fm4dd/pi-weather/documentation/weather-display-v1.0/images/weather-display-v10-09.jpg

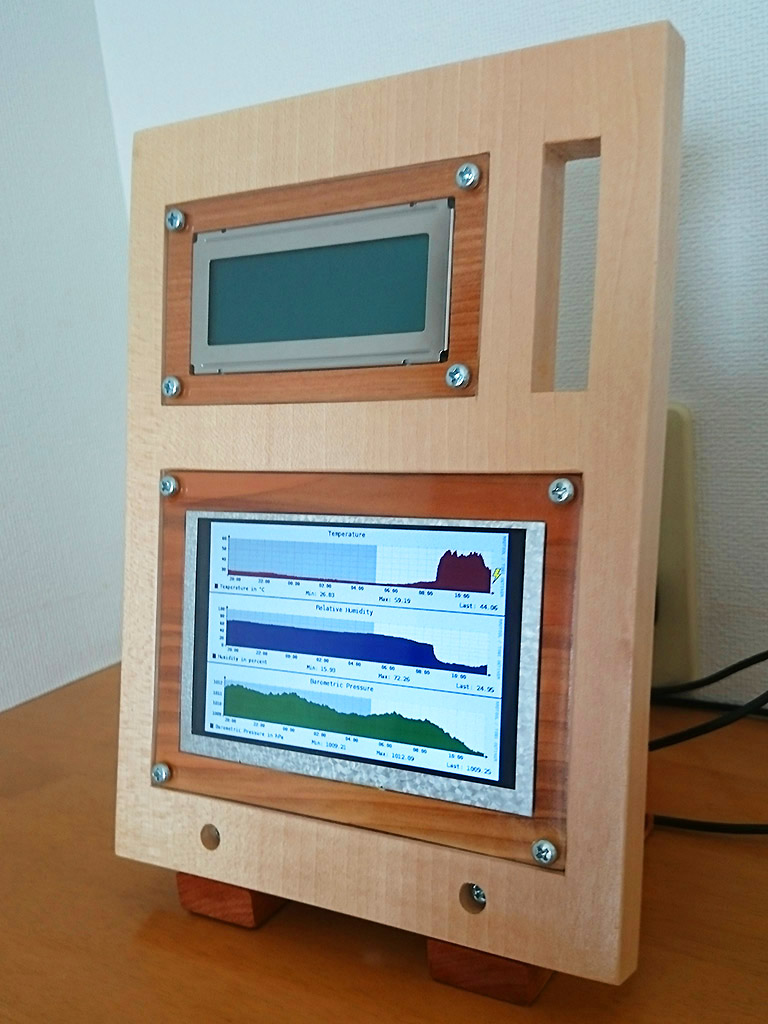
documentation/weather-display-v1.0/images/weather-display-v10-09.jpg
