fm4dd/pi-weather/documentation/weather-station-v1.1/images/weather-station-v11-05.jpg

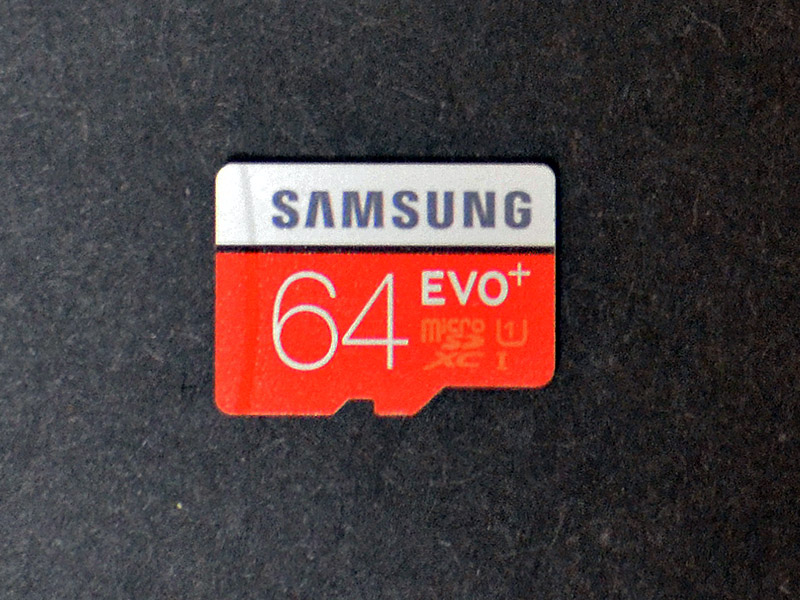
documentation/weather-station-v1.1/images/weather-station-v11-05.jpg
