fm4dd/pi-weather/documentation/weather-web-v1.0/images/weather-web-v10-01.png

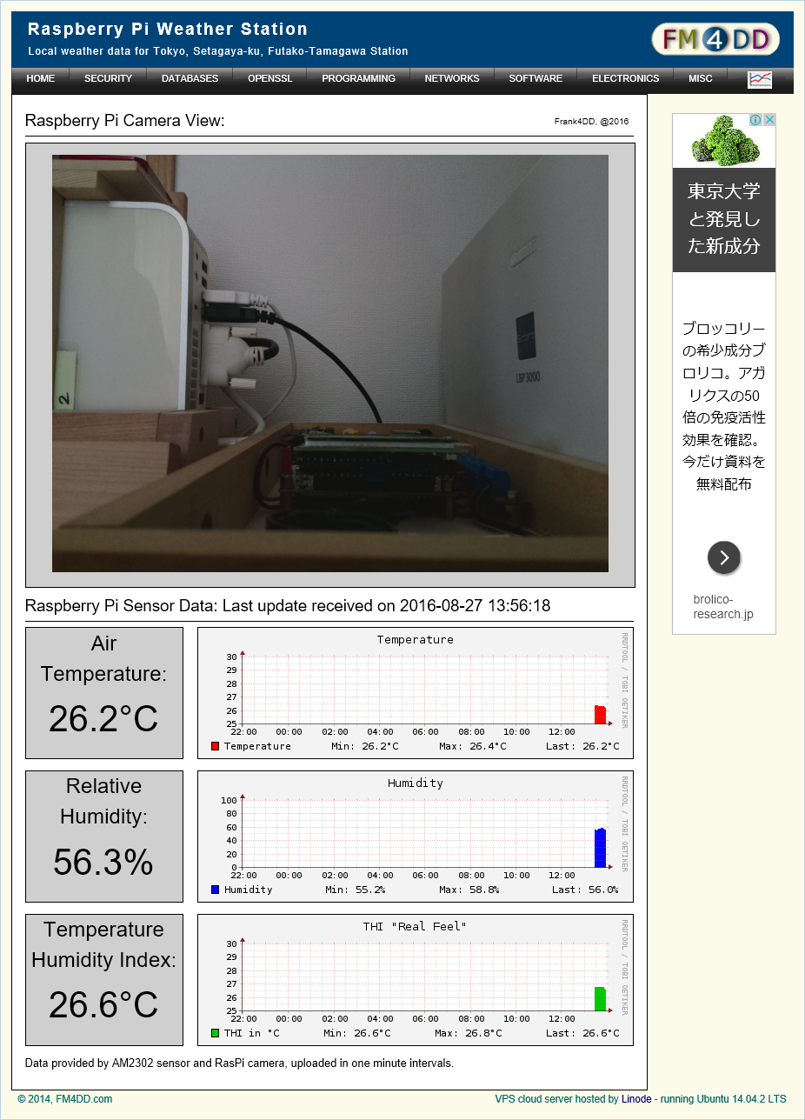
documentation/weather-web-v1.0/images/weather-web-v10-01.png
