fm4dd/pi-weather/weather-display/var/out.png

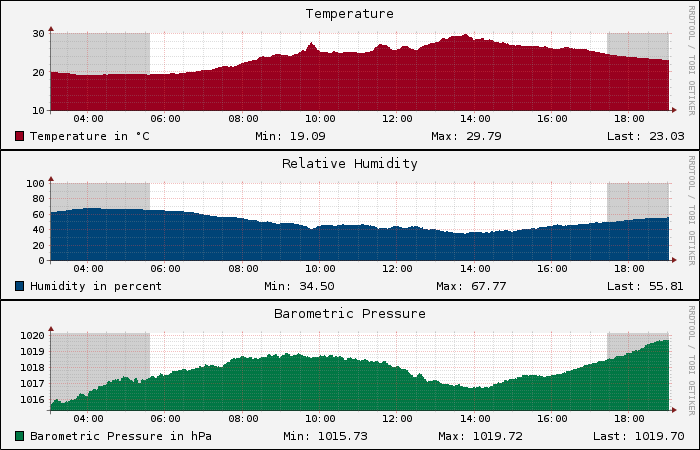
weather-display/var/out.png
