fm4dd/pi-weather/documentation/weather-display-v1.0/cad/05 LCD Frame F and TFT back G v10.dxf

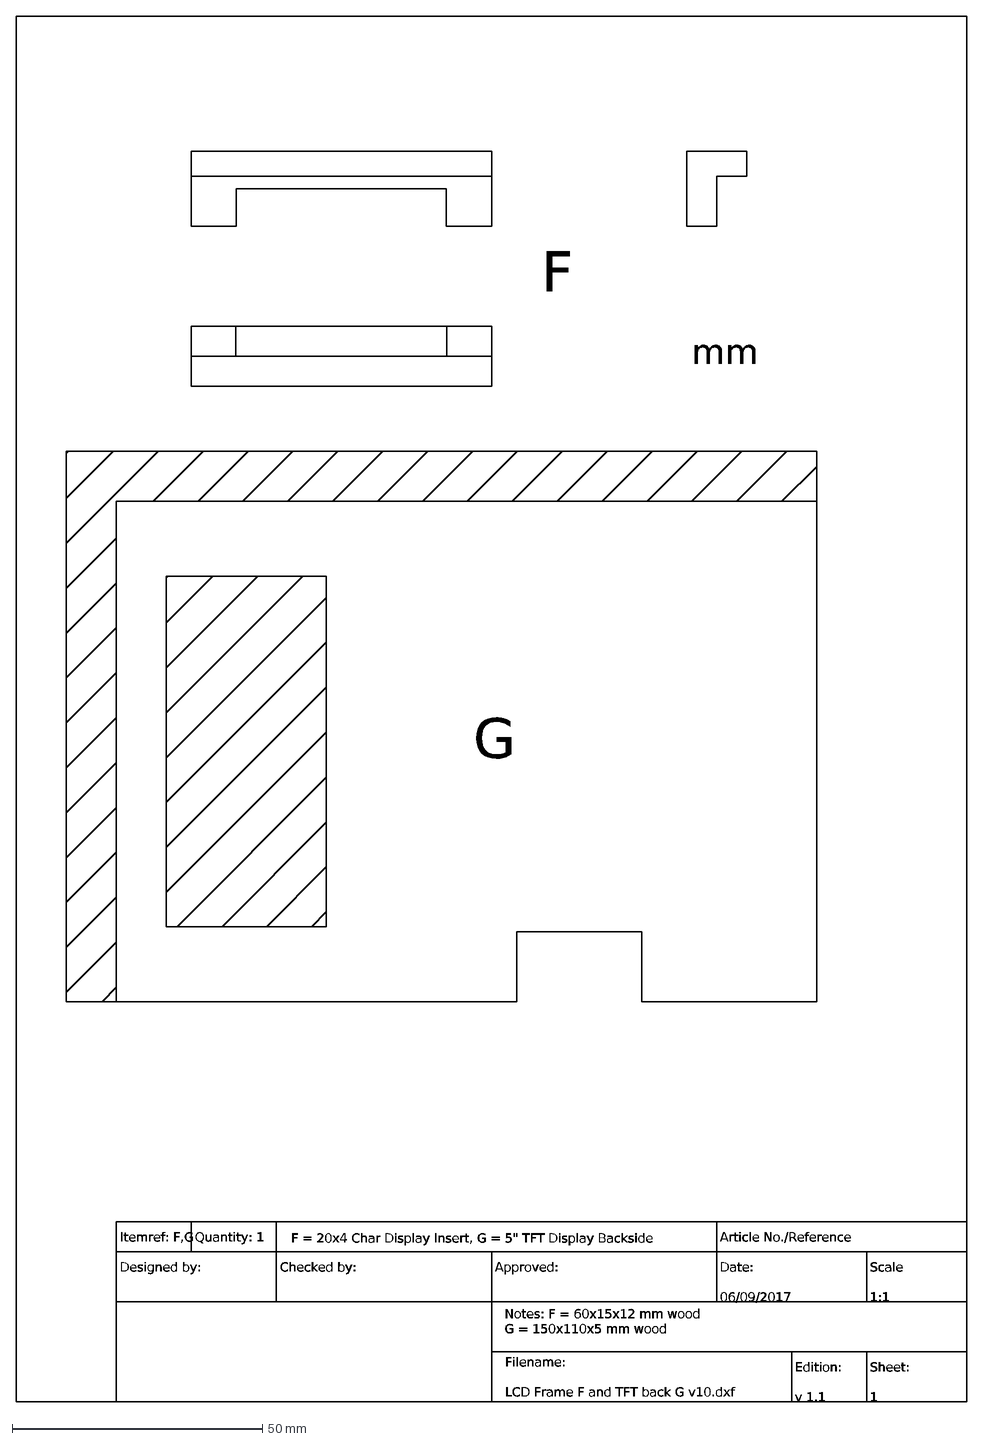
[picture p50: CAD file, 2017-10-29]
documentation/weather-display-v1.0/cad/05 LCD Frame F and TFT back G v10.dxf
Itemref: F,G
Quantity: 1
F = 20x4 Char Display Insert, G = 5" TFT Display Backside
Article No./Reference
Designed by:
Checked by:
Approved:
Filename: LCD Frame F and TFT back G v10.dxf
Date: 06/09/2017
Scale 1:1
Edition: v 1.1
Sheet: 1
Notes: F = 60x15x12 mm wood G = 150x110x5 mm wood
mm
F
G
