fm4dd/pi-weather/documentation/weather-station-v1.1/cad/sensor-frame side detail v11.dxf

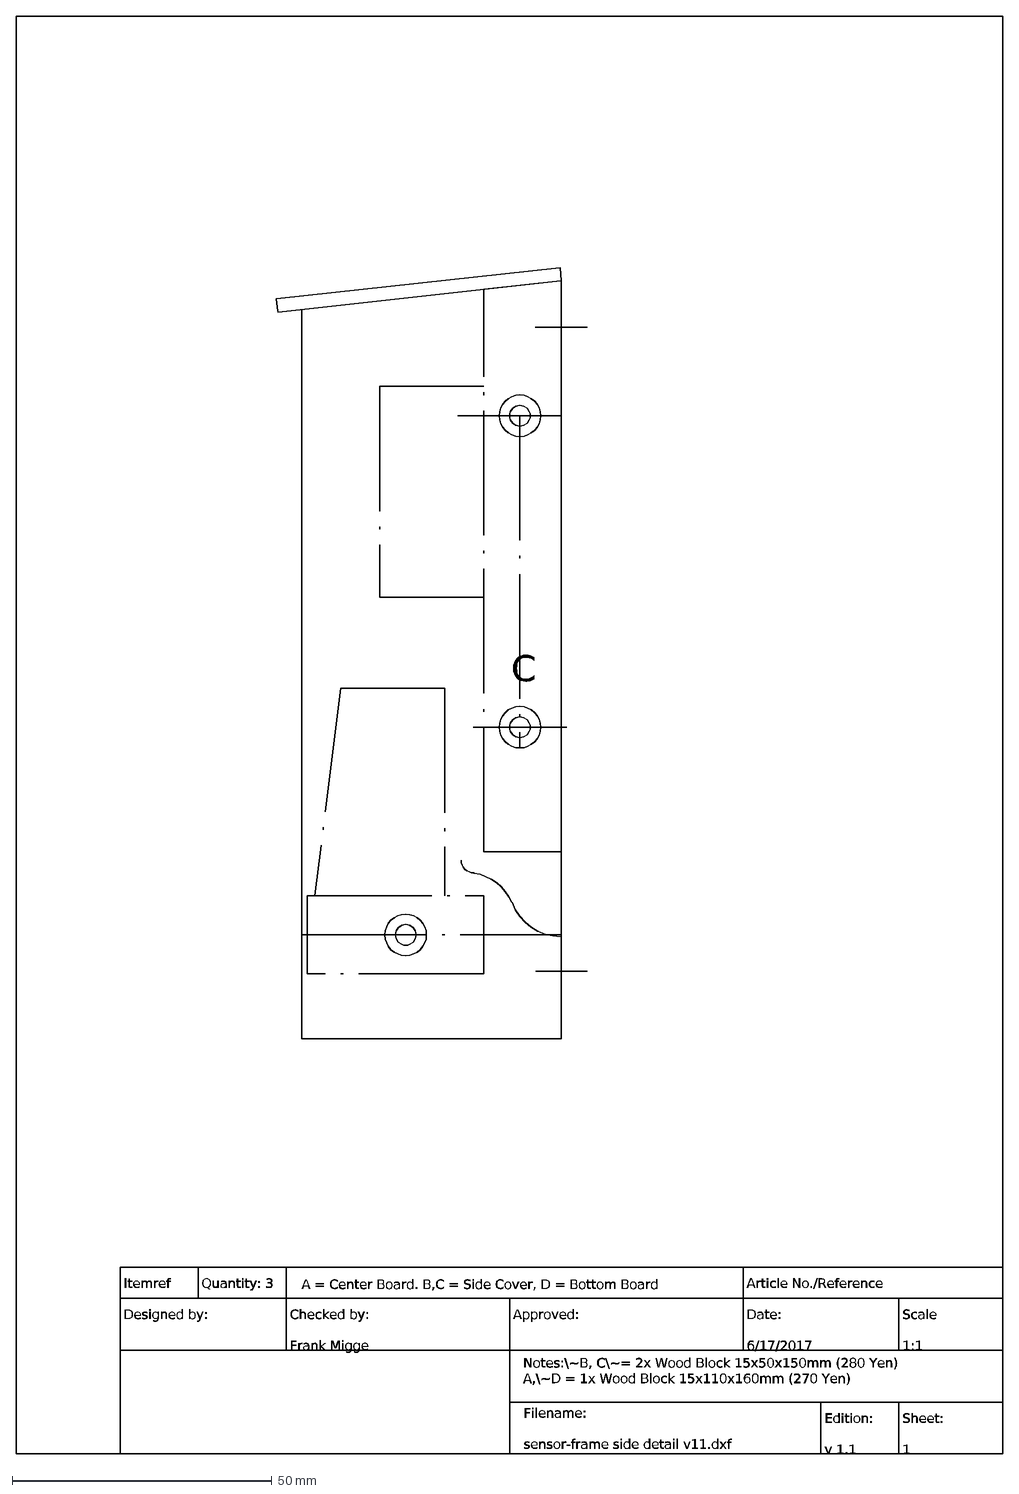
[picture p51: CAD file, 2017-10-29]
documentation/weather-station-v1.1/cad/sensor-frame side detail v11.dxf
Itemref
Quantity: 3
A = Center Board. B,C = Side Cover, D = Bottom Board
Article No./Reference
Designed by:
Checked by: Frank Migge
Approved:
Filename: sensor-frame side detail v11.dxf
Date: 6/17/2017
Scale 1:1
Edition: v 1.1
Sheet: 1
Notes:\~B, C\~= 2x Wood Block 15x50x150mm (280 Yen) A,\~D = 1x Wood Block 15x110x160mm (270 Yen)
C
