fm4dd/pi-weather/documentation/weather-station-v1.0/cad/sensor-frame front detail v10.dxf

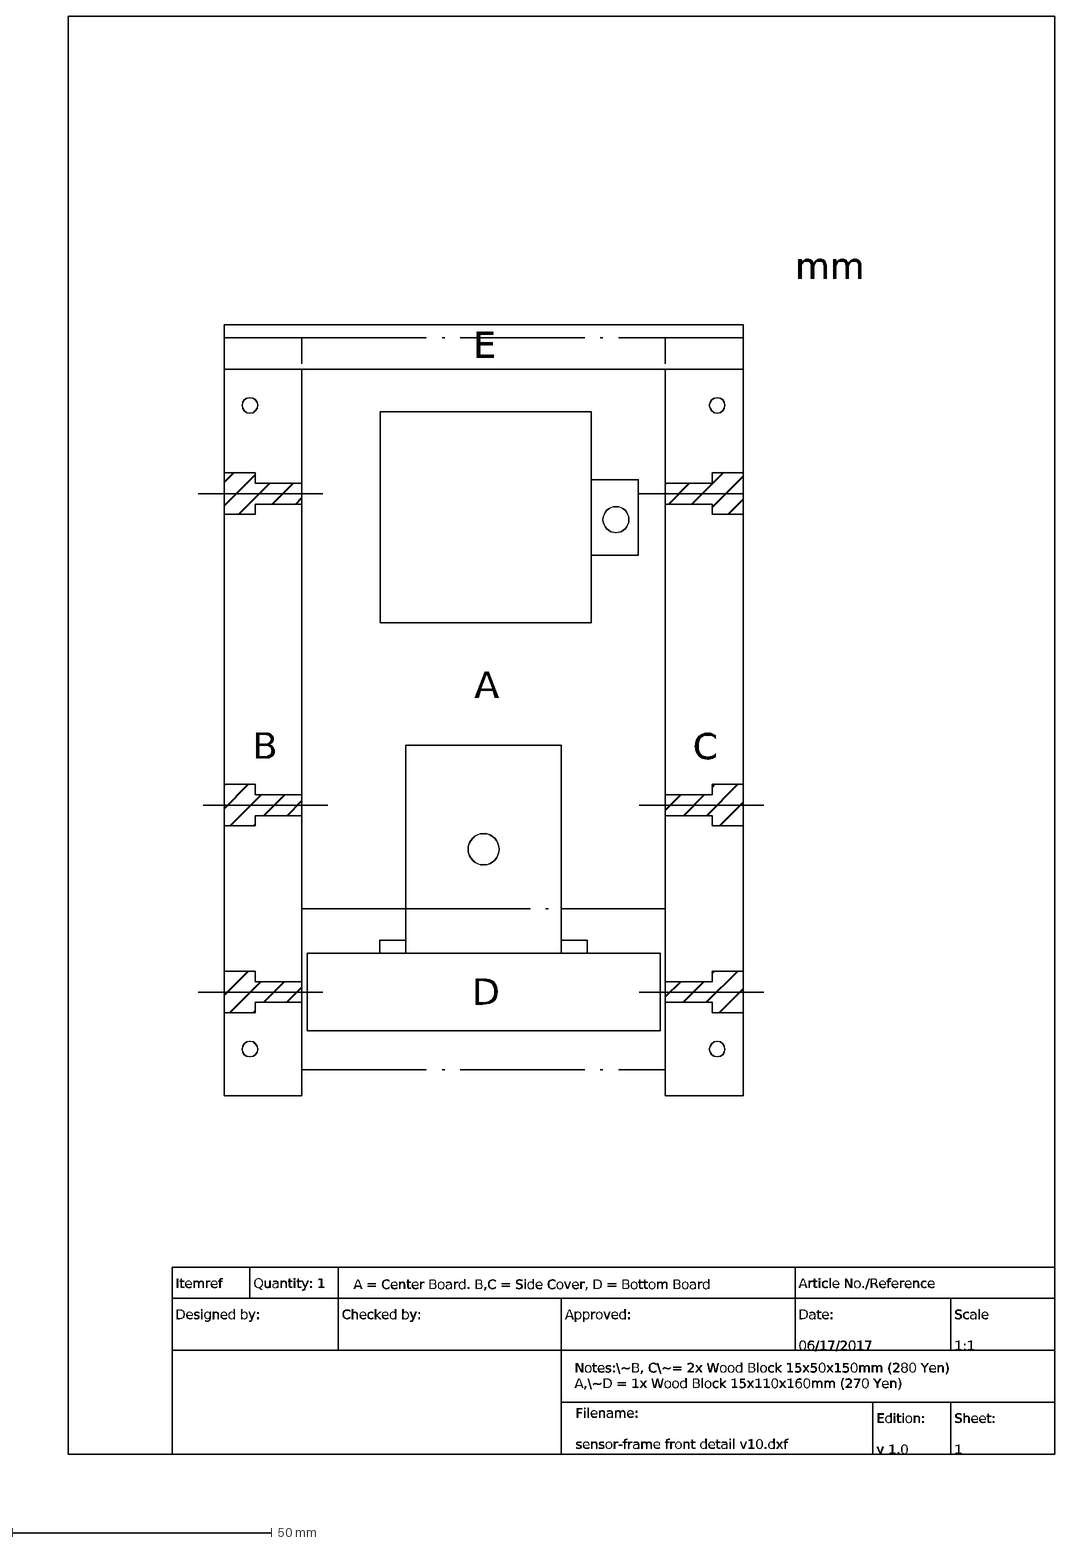
[picture p52: CAD file, 2017-10-29, an earlier design]
documentation/weather-station-v1.0/cad/sensor-frame front detail v10.dxf
Itemref
Quantity: 1
A = Center Board. B,C = Side Cover, D = Bottom Board
Article No./Reference
Designed by:
Checked by:
Approved:
Filename: sensor-frame front detail v10.dxf
Date: 06/17/2017
Scale 1:1
Edition: v 1.0
Sheet: 1
Notes:\~B, C\~= 2x Wood Block 15x50x150mm (280 Yen) A,\~D = 1x Wood Block 15x110x160mm (270 Yen)
A
C
B
D
E
mm
