fm4dd/pi-weather/documentation/weather-station-v1.0/cad/sensor-frame left side v10.dxf

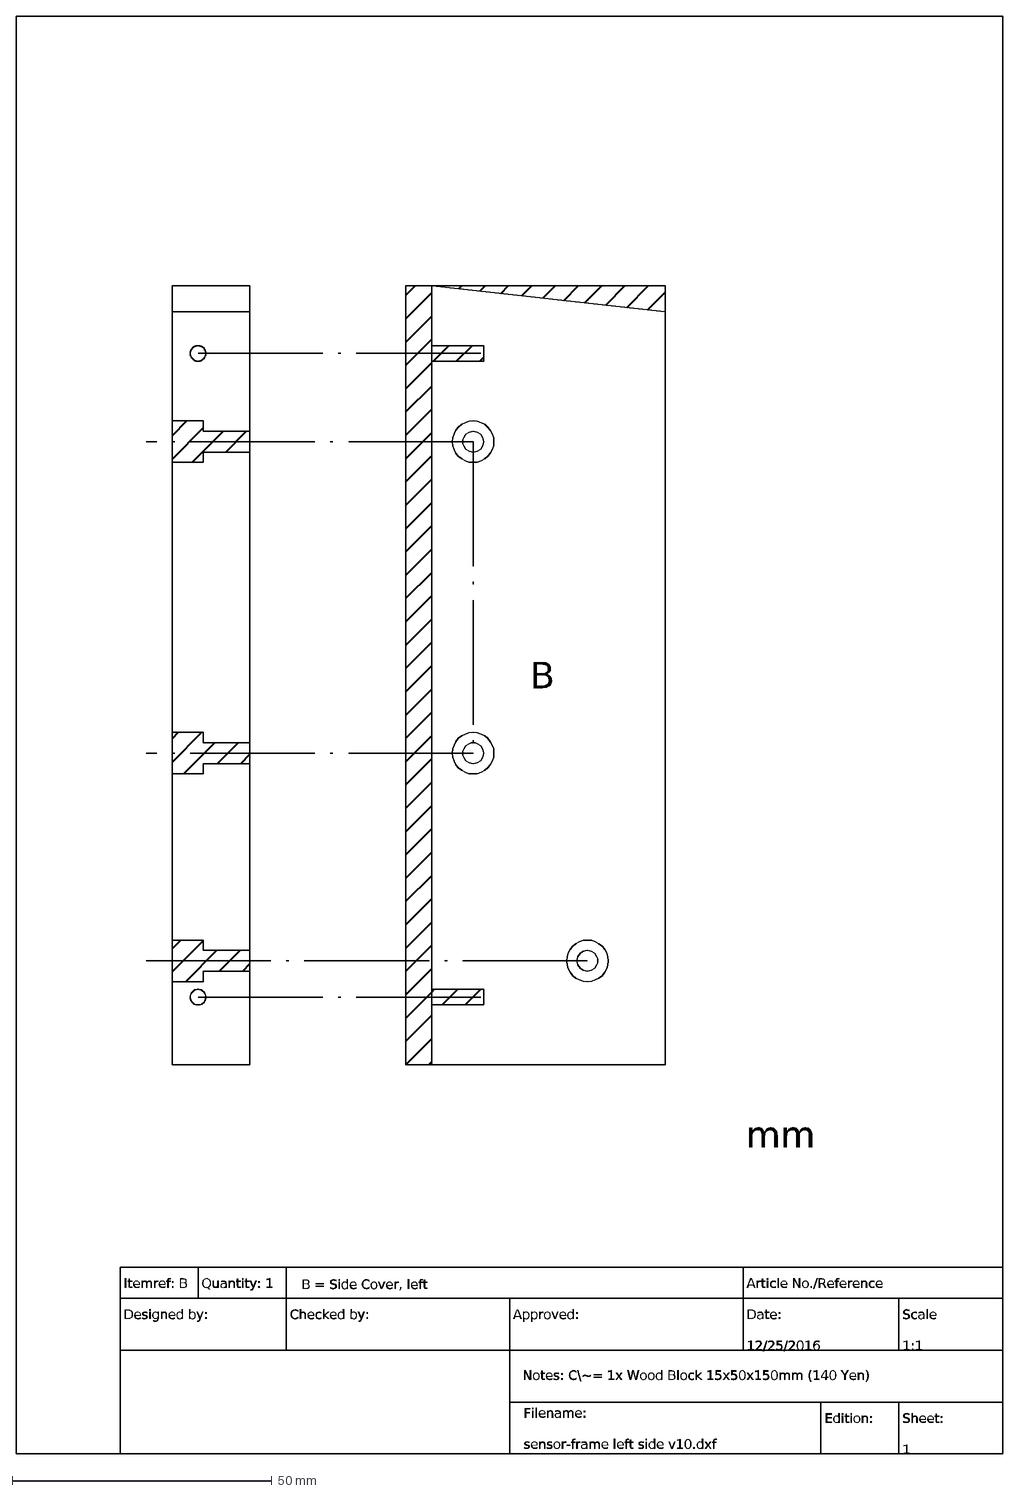
[picture p53: CAD file, 2017-10-29, an earlier design]
documentation/weather-station-v1.0/cad/sensor-frame left side v10.dxf
Itemref: B
Quantity: 1
B = Side Cover, left
Article No./Reference
Designed by:
Checked by:
Approved:
Filename: sensor-frame left side v10.dxf
Date: 12/25/2016
Scale 1:1
Edition:\p v 1.0
Sheet: 1
Notes: C\~= 1x Wood Block 15x50x150mm (140 Yen)
mm
B
