fm4dd/pi-weather/documentation/weather-station-v1.1/cad/sensor-frame front detail v11.pdf

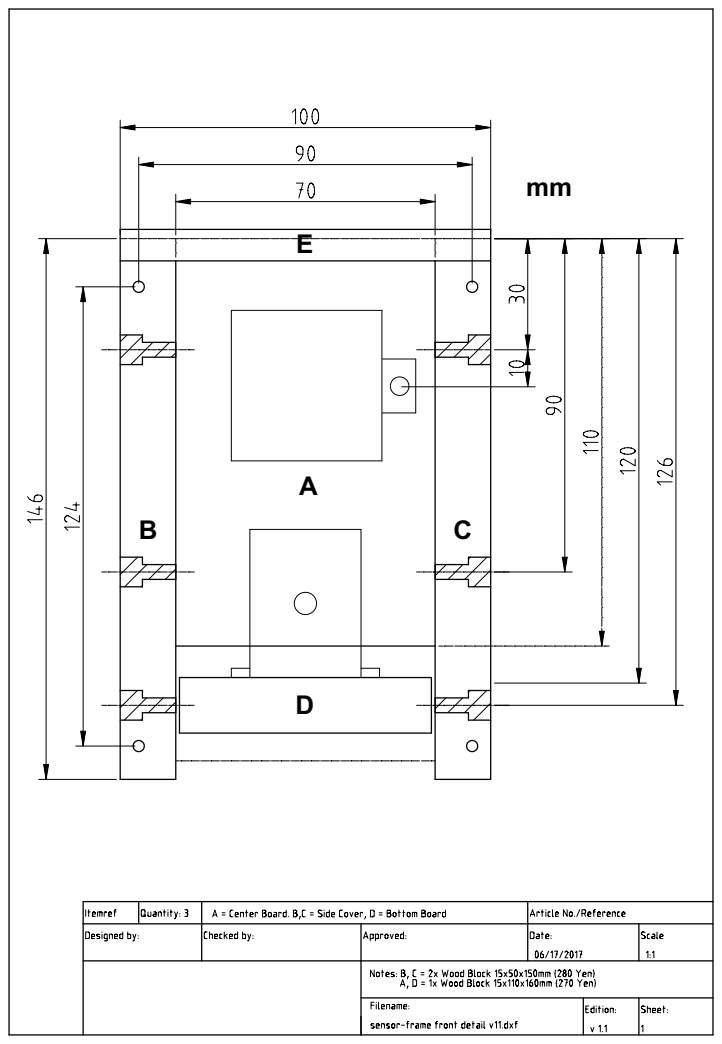
[picture p66: page 1]
