fm4dd/pi-weather/documentation/weather-station-v1.1/cad/sensor-frame left side v11.pdf

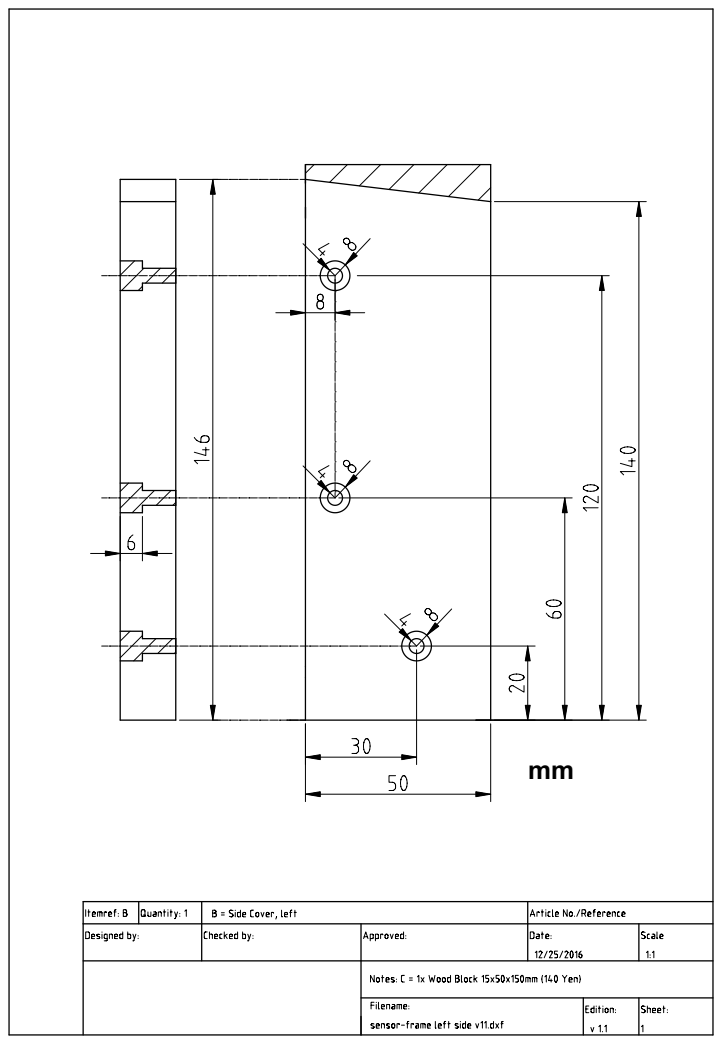
[picture p67: page 1]
