fm4dd/pi-weather/documentation/weather-station-v1.1/cad/sensor-frame right side v11.pdf

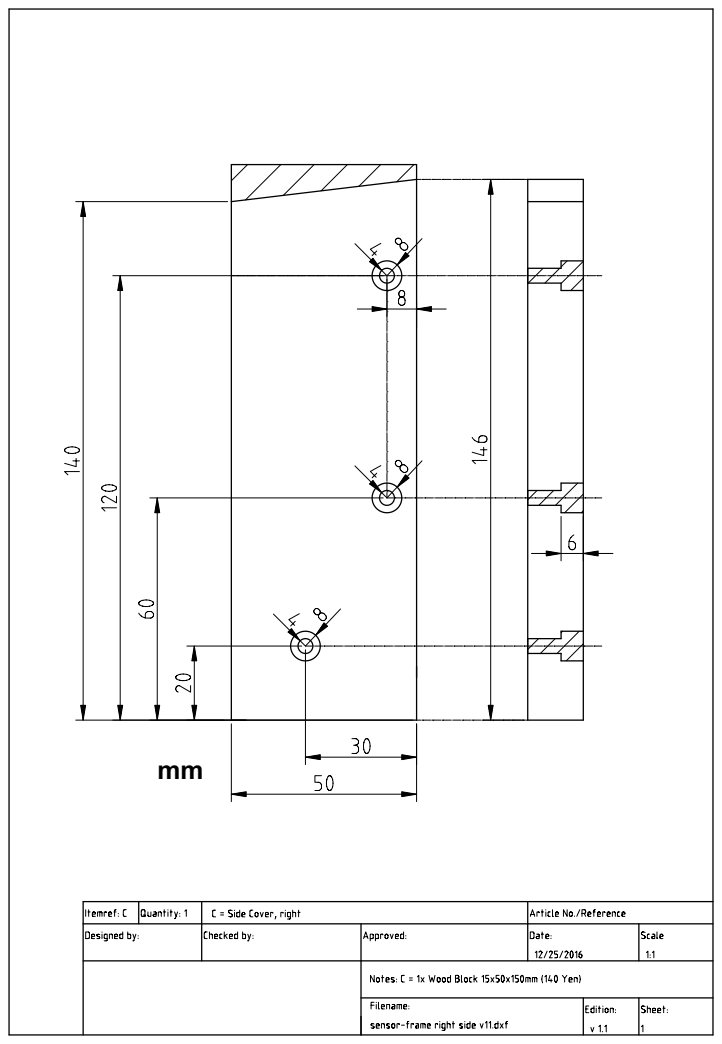
[picture p68: page 1]
