fm4dd/pi-weather/documentation/weather-station-v1.1/cad/sensor-frame side detail v11.pdf

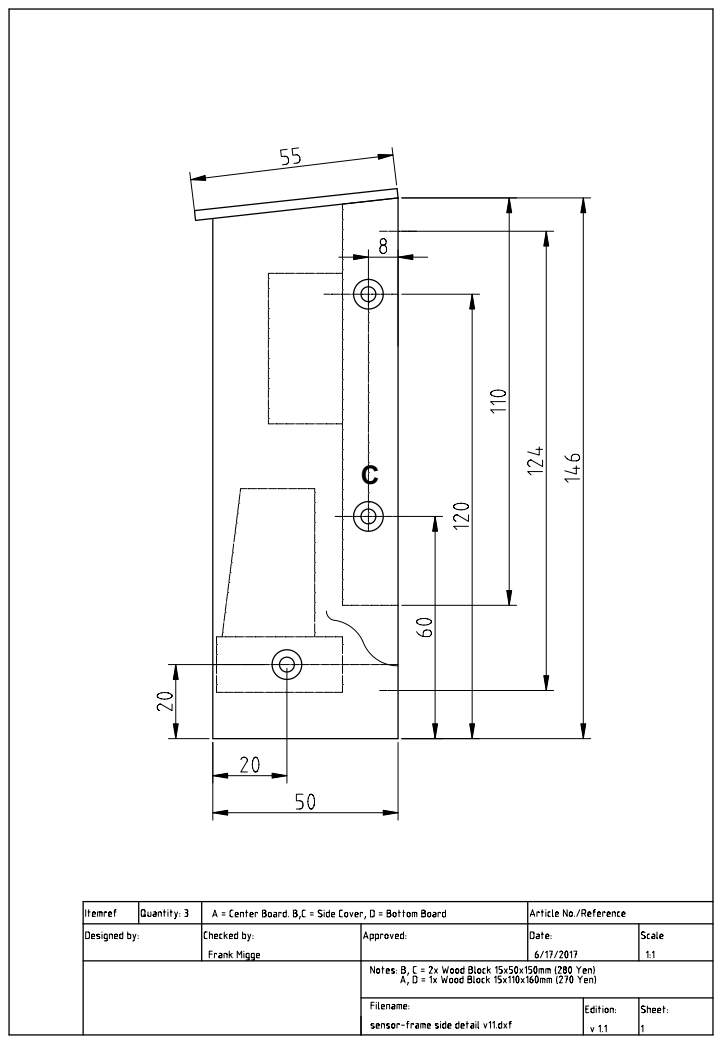
[picture p69: page 1]
