fm4dd/pi-weather/documentation/weather-station-v1.1/cad/sensor-frame top cover v11.pdf

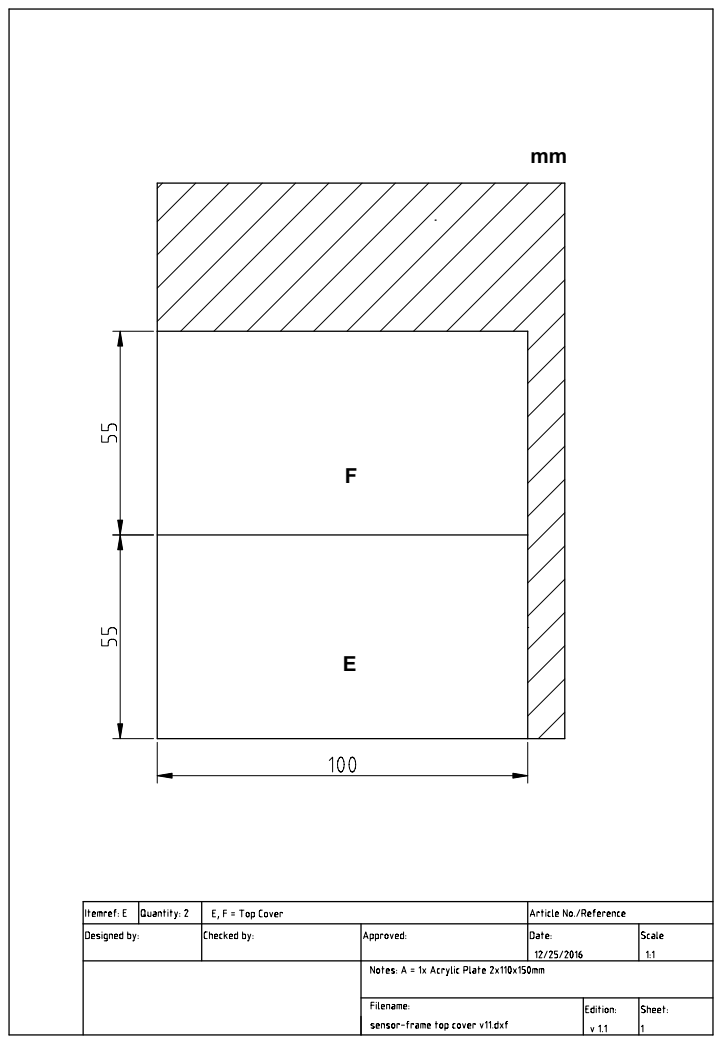
[picture p70: page 1]
