fm4dd/pi-weather/documentation/weather-station-v1.0/cad/sensor-frame center board v10.pdf

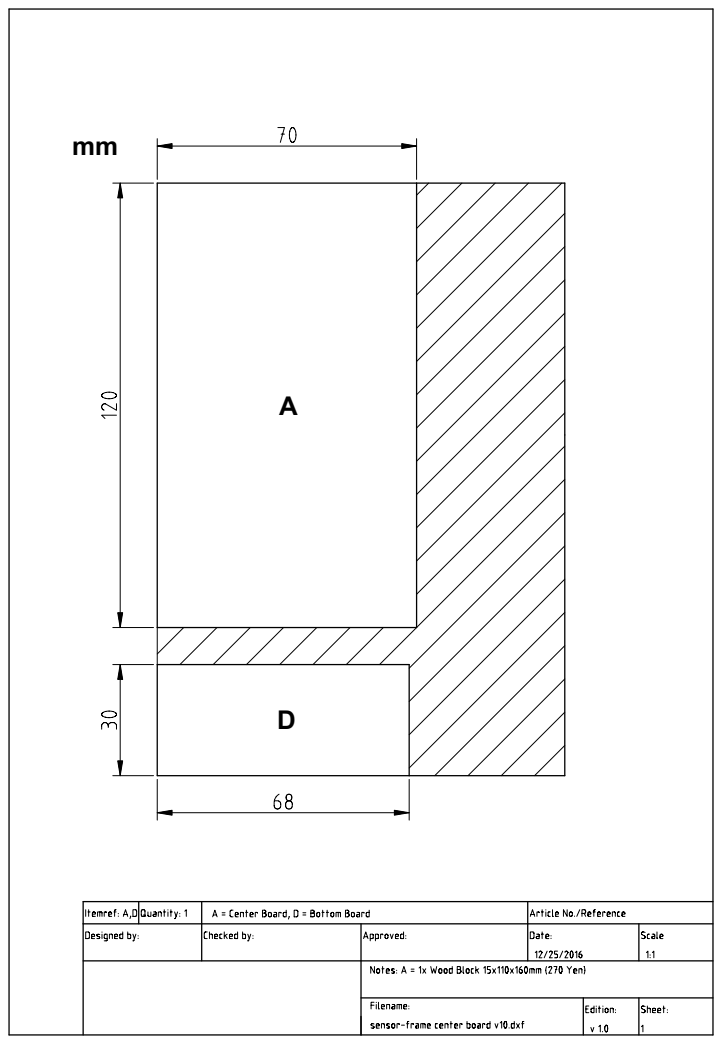
[picture p71: page 1]
