fm4dd/pi-weather/documentation/weather-station-v1.0/cad/sensor-frame front detail v10.pdf

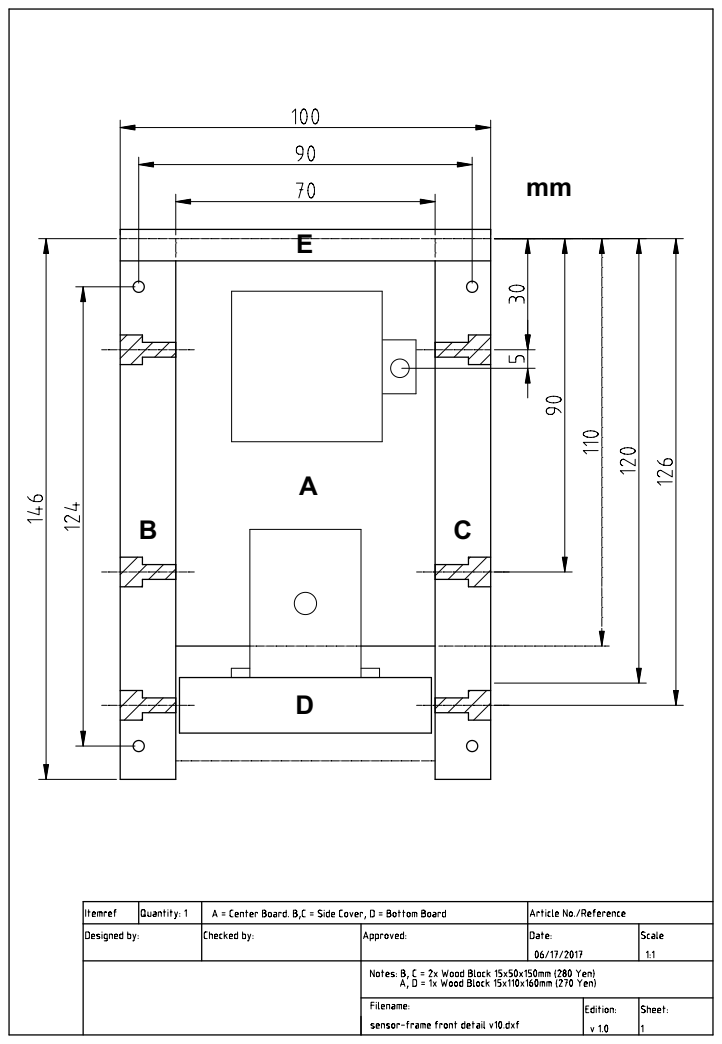
[picture p72: page 1]
