fm4dd/pi-weather/documentation/weather-station-v1.0/cad/sensor-frame left side v10.pdf

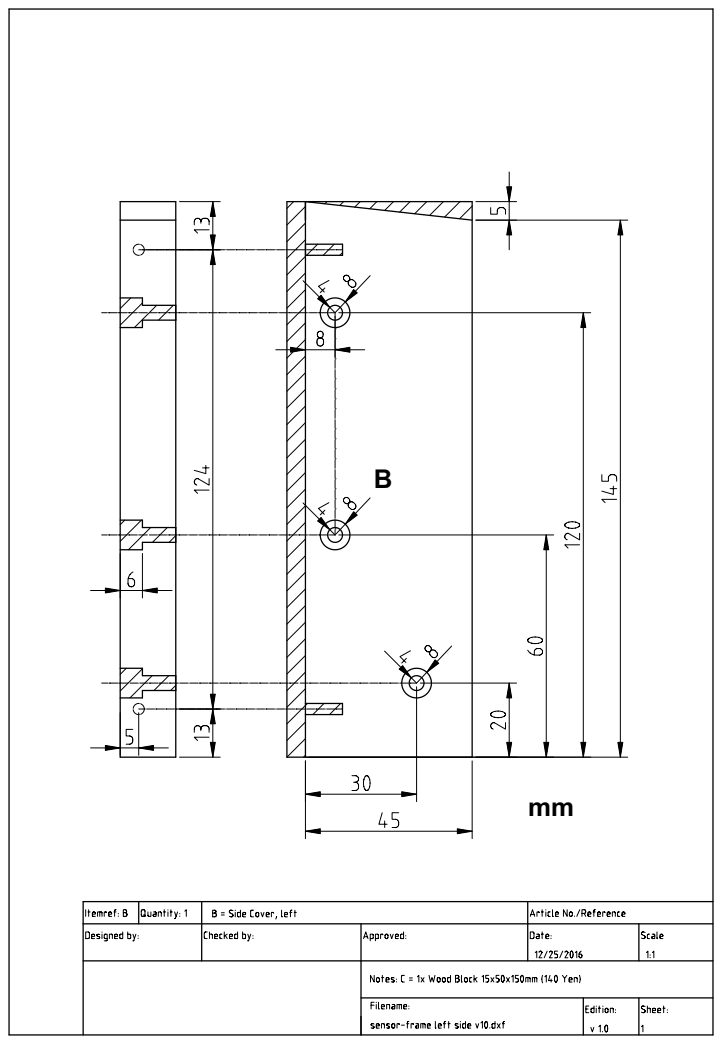
[picture p73: page 1]
