fm4dd/pi-weather/documentation/weather-station-v1.0/cad/sensor-frame right side v10.pdf

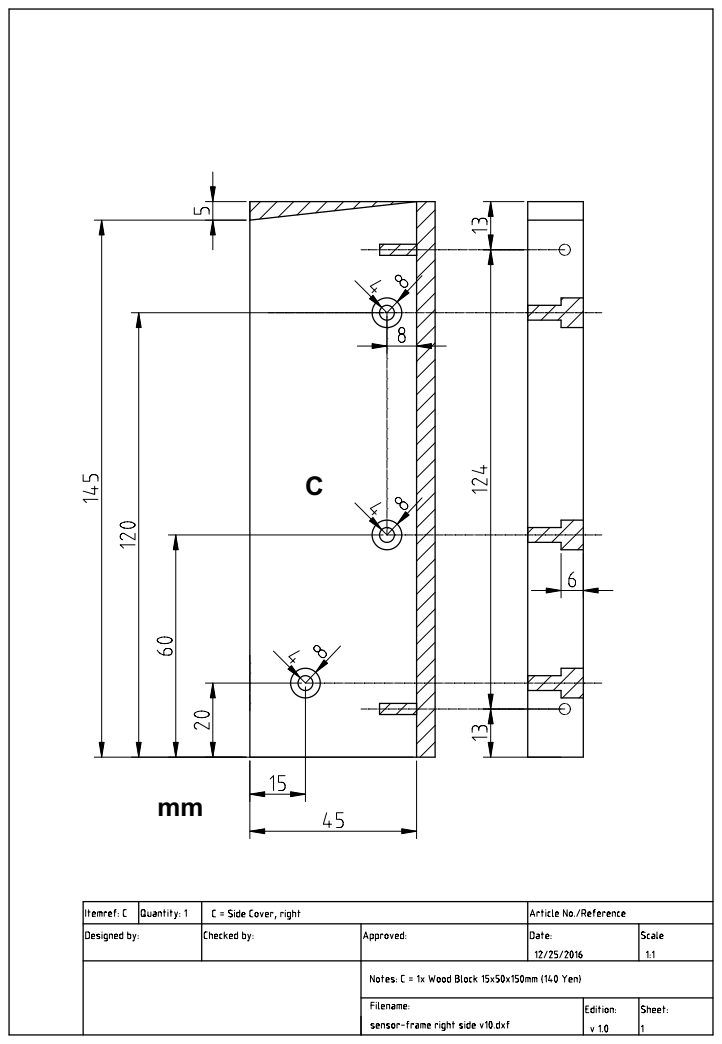
[picture p74: page 1]
