fm4dd/pi-weather/documentation/weather-station-v1.0/cad/sensor-frame side detail v10.pdf

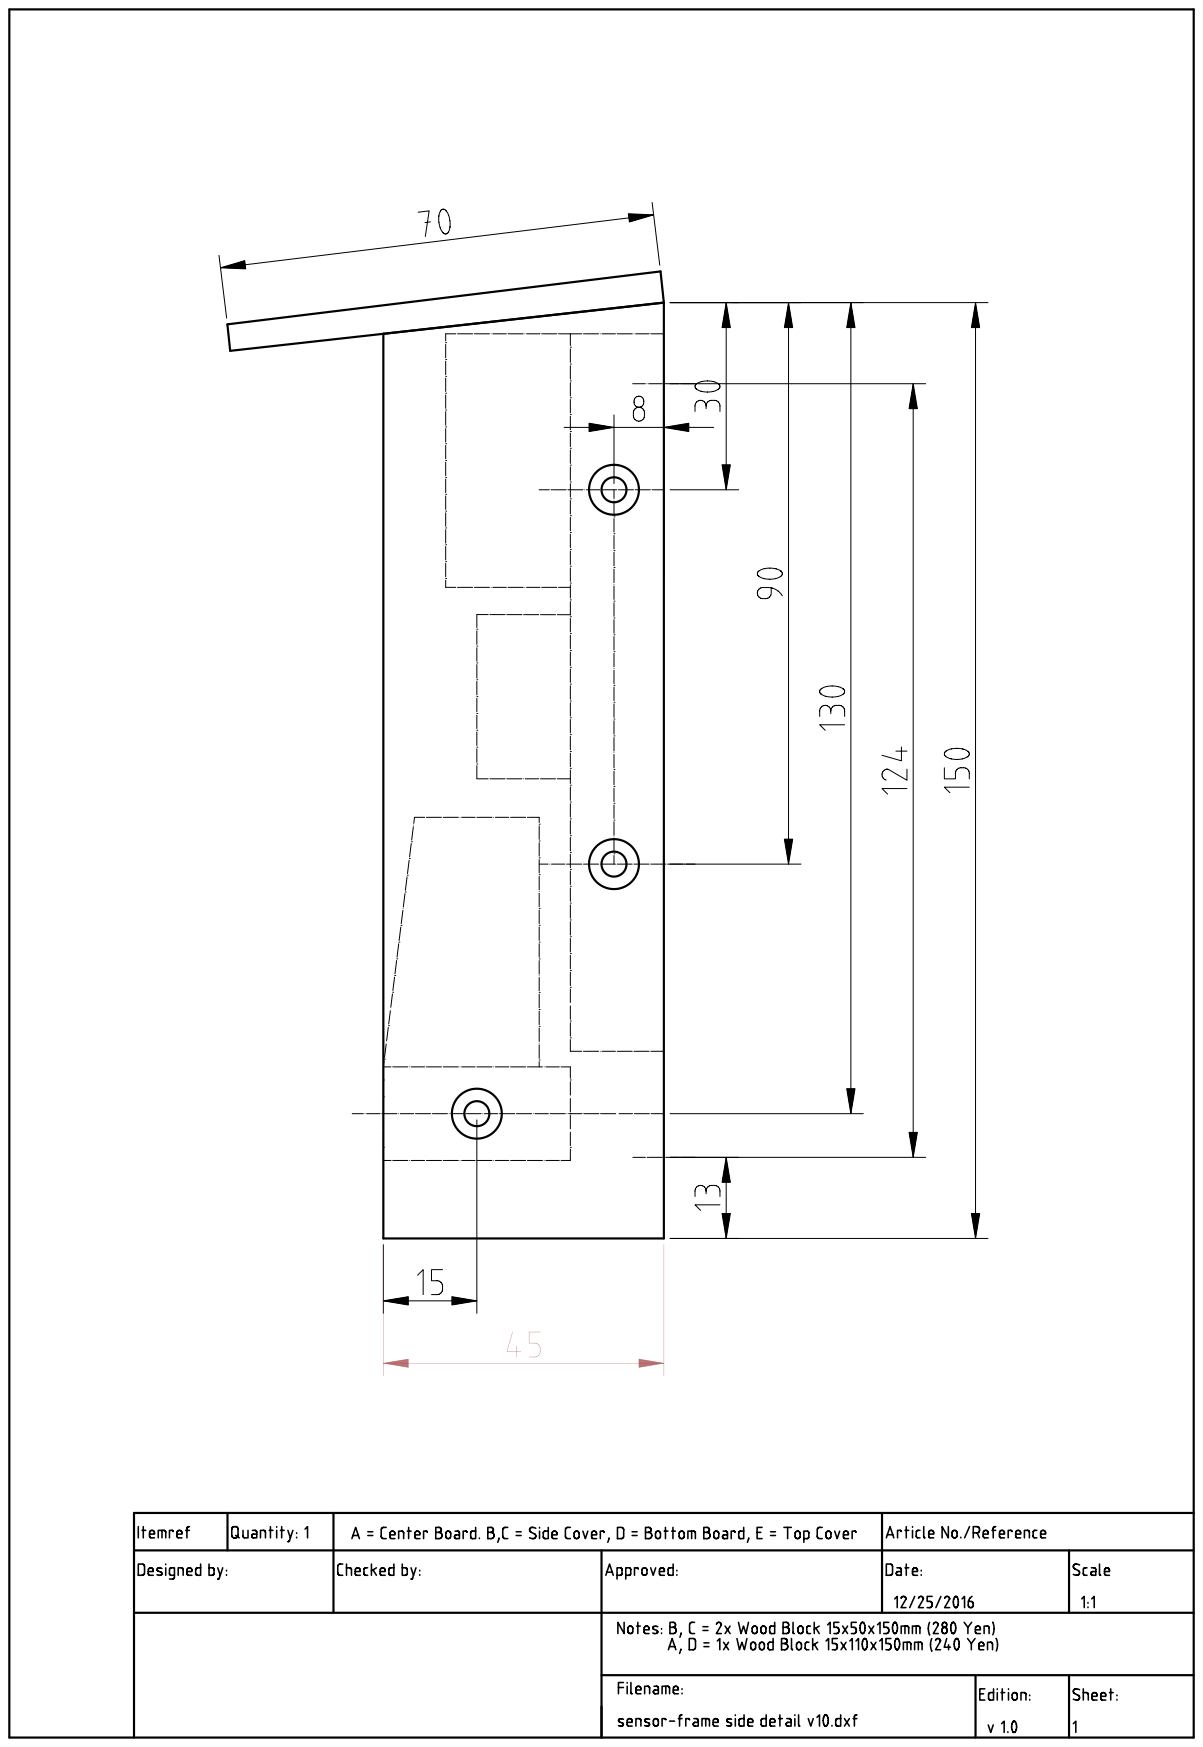
[picture p75: page 1]
