fm4dd/pi-weather/documentation/weather-station-v1.0/cad/sensor-frame top cover v10.pdf

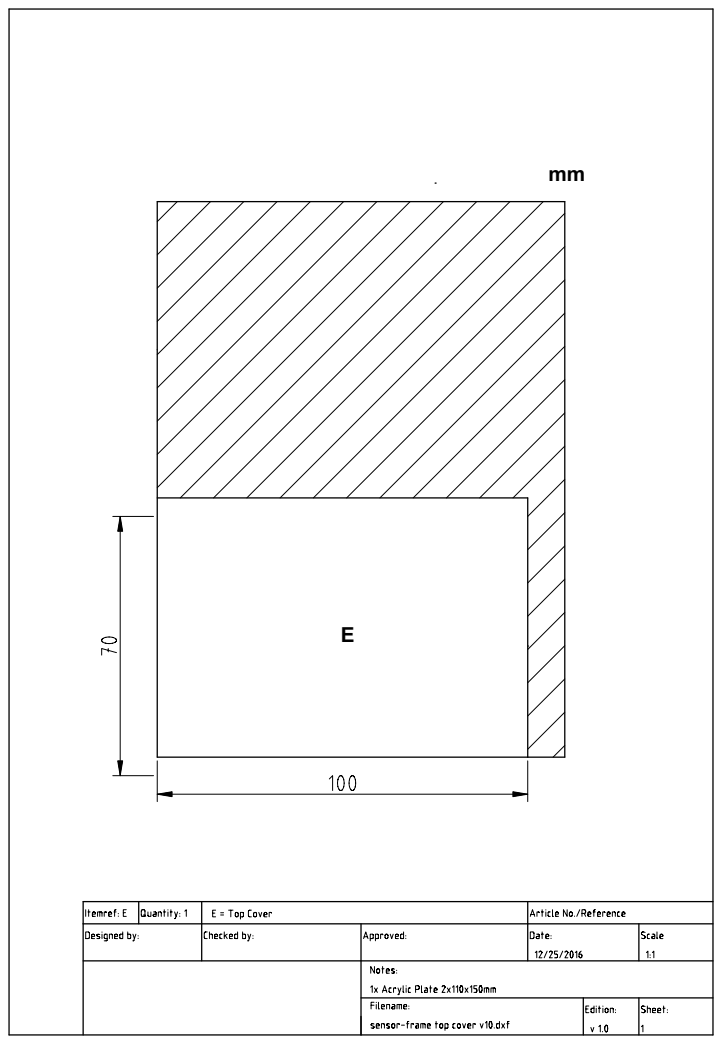
[picture p76: page 1]
