fm4dd/pi-weather/weather-display/bin/sensor.py

#!/usr/bin/env python
# -*- coding: utf-8 -*-

"""
##########################################################
# sensor.py 20170930 Frank4DD
# updated 20220425 for JSON data retrieval over HTTP
# updated 20221204 for weather station access errors
#
# This python3 script manages the 20x4 character LCD
# in combination with the I2C_LCD_driver.py driver.
########################################################
"""
import time
import I2C_LCD_driver
from time import *
import urllib.request
from urllib.error import URLError, HTTPError
from datetime import datetime
import json

# Weather station dowload URL for jsaon sensor data file
ws_url = "http://192.168.11.244/getsensor.json"

try:
   sensor_data = urllib.request.urlopen(ws_url).read().decode('utf-8')
except HTTPError as e:
   err_str = "Error trying to read from " + ws_url + " return code: " + str(e.code)
   print(err_str)
   
try:
   err_str
   now = datetime.now() # current date and time
   line1 = now.strftime("%m/%d/%Y %H:%M:%S")
   line2 = "Error get sensordata"
   line3 = "at 192.168.11.244"
   line4 = "retry in 1 minute"
except NameError:
   #print(sensor_data)
   sensor_obj = json.loads(sensor_data)
   local_time = localtime(sensor_obj["time"])
   timestr = strftime("%D %H:%M", local_time)
   line1 = "Date: " + timestr;
   line2 = "Temp. "+'\xDF'+"C: " + "{0:.2f}".format(sensor_obj["temp"]) + '\xDF'+ "C"
   line3 = "Humidity: " + "{0:.2f}".format(sensor_obj["humi"]) + "%"
   line4 = "Pressure: " + "{0:.2f}".format(sensor_obj["pres"]/100) + "hPa"

#print(line1)
#print(line2)
#print(line3)
#print(line4)
mylcd = I2C_LCD_driver.lcd()
mylcd.lcd_display_string(line1, 1)
mylcd.lcd_display_string(line2, 2)
mylcd.lcd_display_string(line3, 3)
mylcd.lcd_display_string(line4, 4)
